Albert24GG/esp32-bike-computer/raster_tiles_example/Bucharest/16/37474/23684.png

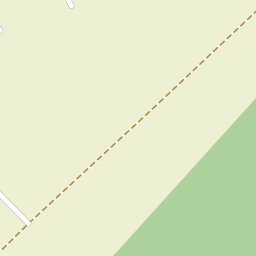
raster_tiles_example/Bucharest/16/37474/23684.png
