Albert24GG/esp32-bike-computer/raster_tiles_example/Bucharest/16/37477/23744.png

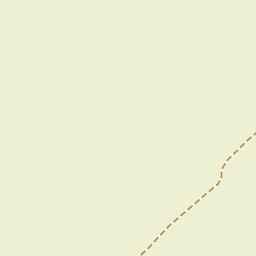
raster_tiles_example/Bucharest/16/37477/23744.png
