Albert24GG/esp32-bike-computer/raster_tiles_example/Bucharest/16/37478/23724.png

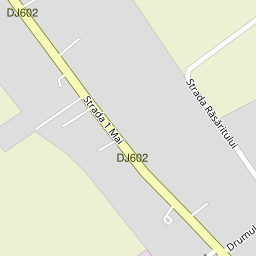
raster_tiles_example/Bucharest/16/37478/23724.png
