Albert24GG/esp32-bike-computer/raster_tiles_example/Bucharest/16/37480/23682.png

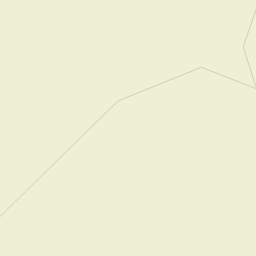
raster_tiles_example/Bucharest/16/37480/23682.png
