Albert24GG/esp32-bike-computer/raster_tiles_example/Bucharest/16/37480/23733.png

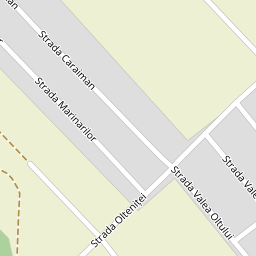
raster_tiles_example/Bucharest/16/37480/23733.png
