Albert24GG/esp32-bike-computer/raster_tiles_example/Bucharest/16/37481/23709.png

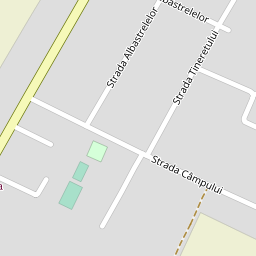
raster_tiles_example/Bucharest/16/37481/23709.png
