Albert24GG/esp32-bike-computer/raster_tiles_example/Bucharest/16/37481/23731.png

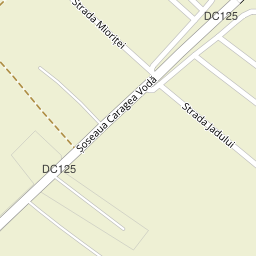
raster_tiles_example/Bucharest/16/37481/23731.png
