Albert24GG/esp32-bike-computer/raster_tiles_example/Bucharest/16/37483/23682.png

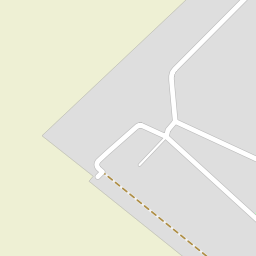
raster_tiles_example/Bucharest/16/37483/23682.png
