Albert24GG/esp32-bike-computer/raster_tiles_example/Bucharest/16/37485/23718.png

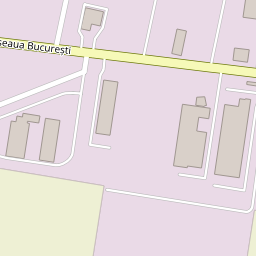
raster_tiles_example/Bucharest/16/37485/23718.png
