Albert24GG/esp32-bike-computer/raster_tiles_example/Bucharest/16/37487/23708.png

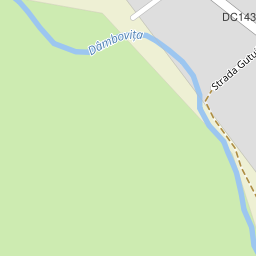
raster_tiles_example/Bucharest/16/37487/23708.png
