Albert24GG/esp32-bike-computer/raster_tiles_example/Bucharest/16/37490/23722.png

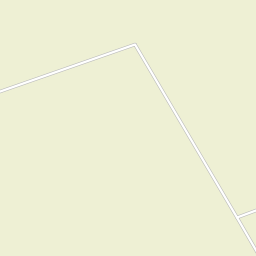
raster_tiles_example/Bucharest/16/37490/23722.png
