Albert24GG/esp32-bike-computer/raster_tiles_example/Bucharest/16/37494/23721.png

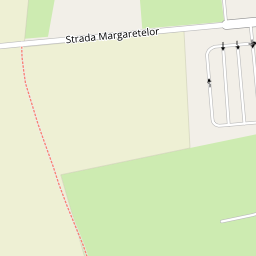
raster_tiles_example/Bucharest/16/37494/23721.png
