Albert24GG/esp32-bike-computer/raster_tiles_example/Bucharest/16/37496/23720.png

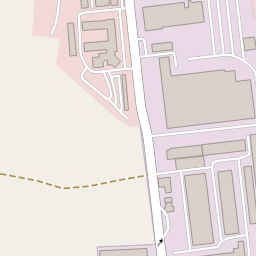
raster_tiles_example/Bucharest/16/37496/23720.png
