Albert24GG/esp32-bike-computer/raster_tiles_example/Bucharest/16/37497/23741.png

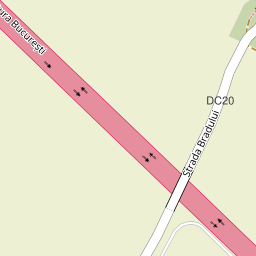
raster_tiles_example/Bucharest/16/37497/23741.png
