Albert24GG/esp32-bike-computer/raster_tiles_example/Bucharest/16/37501/23725.png

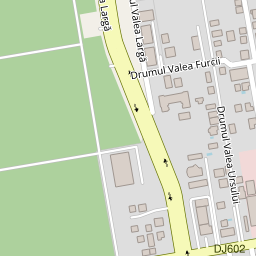
raster_tiles_example/Bucharest/16/37501/23725.png
