Albert24GG/esp32-bike-computer/raster_tiles_example/Bucharest/16/37504/23751.png

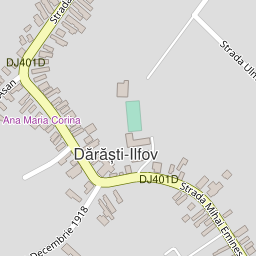
raster_tiles_example/Bucharest/16/37504/23751.png
