Albert24GG/esp32-bike-computer/raster_tiles_example/Bucharest/16/37505/23704.png

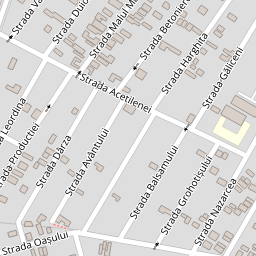
raster_tiles_example/Bucharest/16/37505/23704.png
