Albert24GG/esp32-bike-computer/raster_tiles_example/Bucharest/16/37506/23711.png

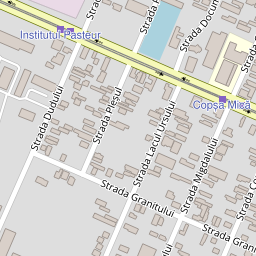
raster_tiles_example/Bucharest/16/37506/23711.png
