Albert24GG/esp32-bike-computer/raster_tiles_example/Bucharest/16/37507/23678.png

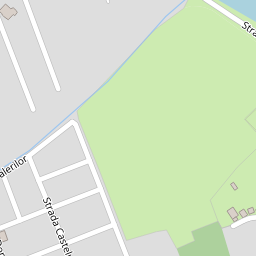
raster_tiles_example/Bucharest/16/37507/23678.png
