Albert24GG/esp32-bike-computer/raster_tiles_example/Bucharest/16/37511/23693.png

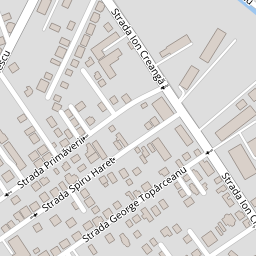
raster_tiles_example/Bucharest/16/37511/23693.png
