Albert24GG/esp32-bike-computer/raster_tiles_example/Bucharest/16/37512/23710.png

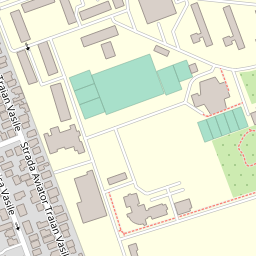
raster_tiles_example/Bucharest/16/37512/23710.png
