Albert24GG/esp32-bike-computer/raster_tiles_example/Bucharest/16/37514/23737.png

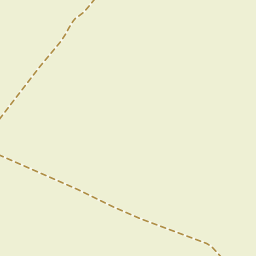
raster_tiles_example/Bucharest/16/37514/23737.png
