Albert24GG/esp32-bike-computer/raster_tiles_example/Bucharest/16/37515/23697.png

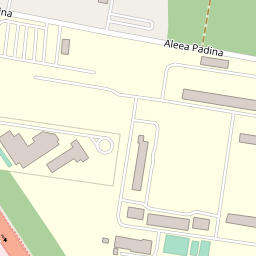
raster_tiles_example/Bucharest/16/37515/23697.png
