Albert24GG/esp32-bike-computer/raster_tiles_example/Bucharest/16/37516/23734.png

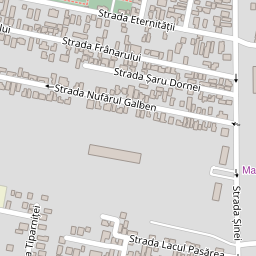
raster_tiles_example/Bucharest/16/37516/23734.png
