Albert24GG/esp32-bike-computer/raster_tiles_example/Bucharest/16/37519/23688.png

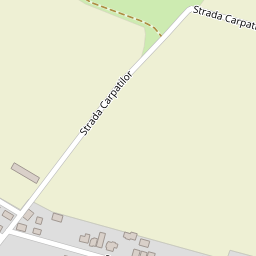
raster_tiles_example/Bucharest/16/37519/23688.png
