Albert24GG/esp32-bike-computer/raster_tiles_example/Bucharest/16/37520/23701.png

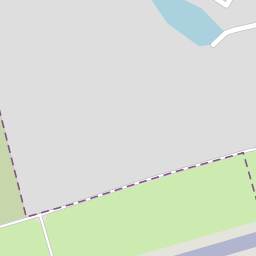
raster_tiles_example/Bucharest/16/37520/23701.png
