Albert24GG/esp32-bike-computer/raster_tiles_example/Bucharest/16/37520/23742.png

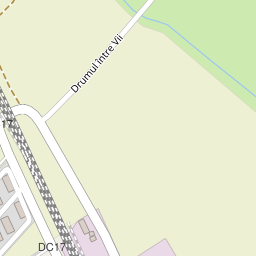
raster_tiles_example/Bucharest/16/37520/23742.png
