Albert24GG/esp32-bike-computer/raster_tiles_example/Bucharest/16/37522/23714.png

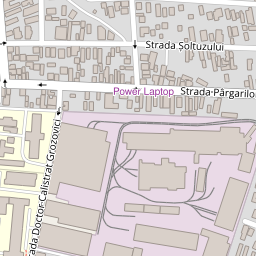
raster_tiles_example/Bucharest/16/37522/23714.png
