Albert24GG/esp32-bike-computer/raster_tiles_example/Bucharest/16/37523/23749.png

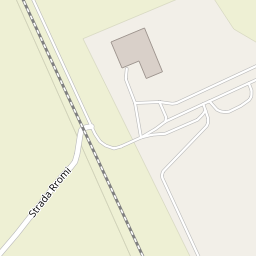
raster_tiles_example/Bucharest/16/37523/23749.png
