Albert24GG/esp32-bike-computer/raster_tiles_example/Bucharest/16/37525/23686.png

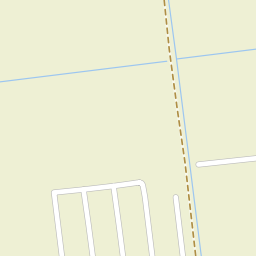
raster_tiles_example/Bucharest/16/37525/23686.png
