Albert24GG/esp32-bike-computer/raster_tiles_example/Bucharest/16/37526/23726.png

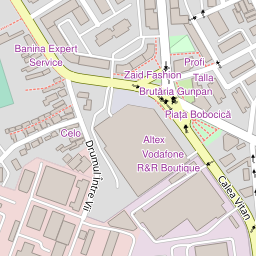
raster_tiles_example/Bucharest/16/37526/23726.png
