Albert24GG/esp32-bike-computer/raster_tiles_example/Bucharest/16/37530/23736.png

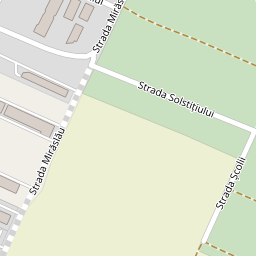
raster_tiles_example/Bucharest/16/37530/23736.png
