Albert24GG/esp32-bike-computer/raster_tiles_example/Bucharest/16/37531/23731.png

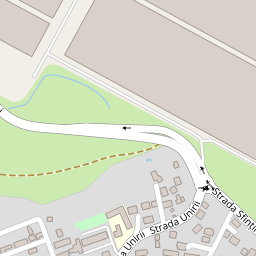
raster_tiles_example/Bucharest/16/37531/23731.png
