Albert24GG/esp32-bike-computer/raster_tiles_example/Bucharest/16/37532/23713.png

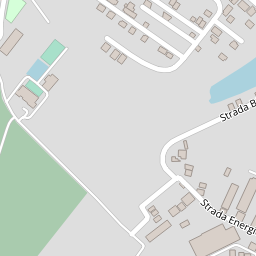
raster_tiles_example/Bucharest/16/37532/23713.png
