Albert24GG/esp32-bike-computer/raster_tiles_example/Bucharest/16/37536/23753.png

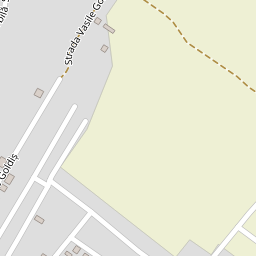
raster_tiles_example/Bucharest/16/37536/23753.png
