Albert24GG/esp32-bike-computer/raster_tiles_example/Bucharest/16/37539/23723.png

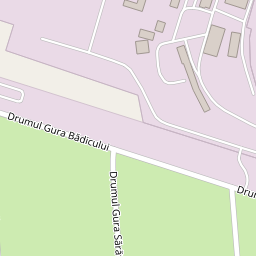
raster_tiles_example/Bucharest/16/37539/23723.png
