Albert24GG/esp32-bike-computer/raster_tiles_example/Bucharest/16/37540/23687.png

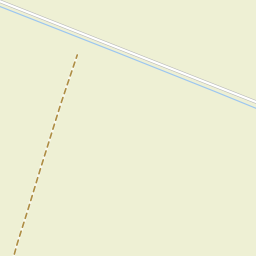
raster_tiles_example/Bucharest/16/37540/23687.png
