Albert24GG/esp32-bike-computer/raster_tiles_example/Bucharest/16/37542/23728.png

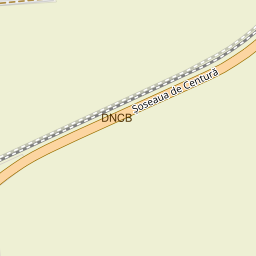
raster_tiles_example/Bucharest/16/37542/23728.png
