Albert24GG/esp32-bike-computer/raster_tiles_example/Bucharest/16/37543/23694.png

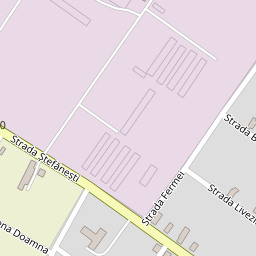
raster_tiles_example/Bucharest/16/37543/23694.png
