Albert24GG/esp32-bike-computer/raster_tiles_example/Bucharest/16/37545/23691.png

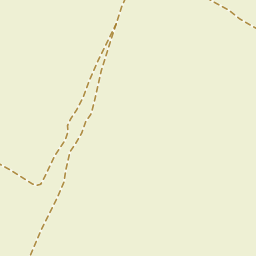
raster_tiles_example/Bucharest/16/37545/23691.png
