Albert24GG/esp32-bike-computer/raster_tiles_example/Bucharest/16/37547/23703.png

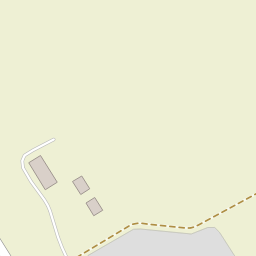
raster_tiles_example/Bucharest/16/37547/23703.png
