Albert24GG/esp32-bike-computer/raster_tiles_example/Bucharest/16/37551/23746.png

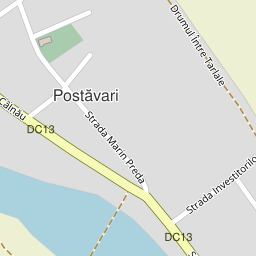
raster_tiles_example/Bucharest/16/37551/23746.png
