Albert24GG/esp32-bike-computer/raster_tiles_example/Bucharest/16/37554/23729.png

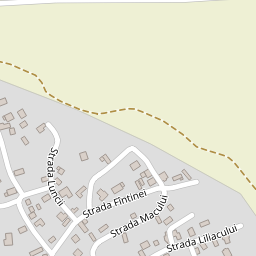
raster_tiles_example/Bucharest/16/37554/23729.png
