Albert24GG/esp32-bike-computer/raster_tiles_example/Bucharest/16/37556/23732.png

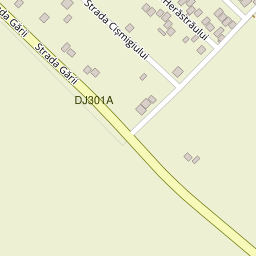
raster_tiles_example/Bucharest/16/37556/23732.png
