Albert24GG/esp32-bike-computer/raster_tiles_example/Bucharest/16/37561/23700.png

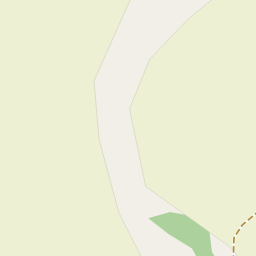
raster_tiles_example/Bucharest/16/37561/23700.png
