Albert24GG/esp32-bike-computer/raster_tiles_example/Bucharest/16/37564/23727.png

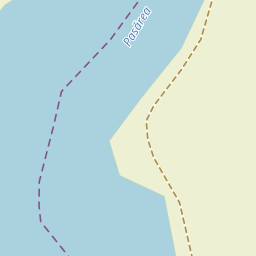
raster_tiles_example/Bucharest/16/37564/23727.png
