Albert24GG/esp32-bike-computer/raster_tiles_example/Bucharest/16/37566/23735.png

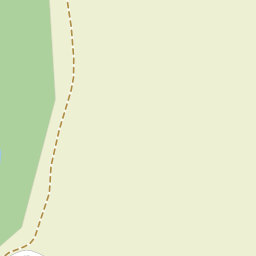
raster_tiles_example/Bucharest/16/37566/23735.png
