Albert24GG/esp32-bike-computer/raster_tiles_example/Bucharest/16/37568/23691.png

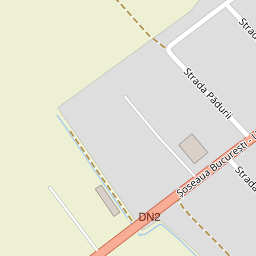
raster_tiles_example/Bucharest/16/37568/23691.png
