Albert24GG/esp32-bike-computer/raster_tiles_example/Bucharest/16/37570/23685.png

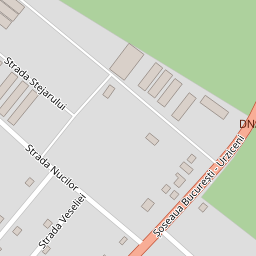
raster_tiles_example/Bucharest/16/37570/23685.png
