Albert24GG/esp32-bike-computer/raster_tiles_example/Bucharest/16/37572/23692.png

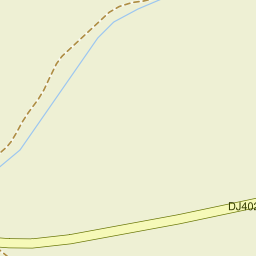
raster_tiles_example/Bucharest/16/37572/23692.png
