Albert24GG/esp32-bike-computer/raster_tiles_example/Bucharest/16/37573/23718.png

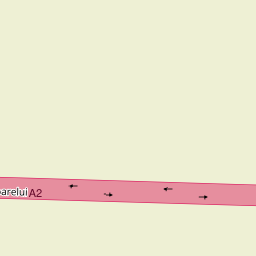
raster_tiles_example/Bucharest/16/37573/23718.png
