Albert24GG/esp32-bike-computer/raster_tiles_example/Bucharest/16/37573/23747.png

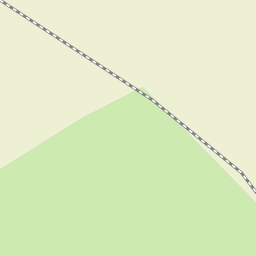
raster_tiles_example/Bucharest/16/37573/23747.png
